ghowoght/mecanum-car/Src/general/dt.h

/**
 * @file dt.h
 * @brief 数据传输程序
 * @author Linfu Wei (ghowoght@qq.com)
 * @version 1.0
 * @date 2020-12-27
 * 
 * @copyright Copyright (c) 2020  WHU-EIS
 * 
 */
#ifndef __DT_H_
#define __DT_H_
#include "stm32g4xx_hal.h"

extern uint8_t data_receive[100];
extern uint8_t data_one_byte[1];
void GetOneByte(uint8_t data);
void DataDecoder(uint8_t *data);

extern UART_HandleTypeDef hlpuart1;
extern UART_HandleTypeDef huart1;
void DataTrans(void);
void DataTrans_IMU_Raw(void);
void DataTrans_UserData(void);
void DataTrans_Odom(void);
void DataTrans_Task(uint32_t dT_ms);


#endif
