ghowoght/mecanum-car/SensorDriver/IIC/IOI2C.h

#ifndef __IOI2C_H
#define __IOI2C_H
#include "sys.h"
 
extern volatile u8 I2C_FastMode;

//IO方向设置
#define SDA_IN()  {GPIOC->MODER&=~(3<<(7*2));GPIOC->MODER|=0<<7*2;}	
#define SDA_OUT() {GPIOC->MODER&=~(3<<(7*2));GPIOC->MODER|=1<<7*2;} 	
//void SDA_IN(void);
//void SDA_OUT(void);


//IO操作函数	 
#define IIC_SCL    PCout(6) //SCL
#define IIC_SDA    PCout(7) //SDA	 
#define READ_SDA   PCin(7)  //输入SDA 

//IIC所有操作函数 
int IIC_Start(void);				//发送IIC开始信号
void IIC_Stop(void);	  			//发送IIC停止信号
void IIC_Send_Byte(u8 txd);			//IIC发送一个字节
u8 IIC_Read_Byte(unsigned char ack);//IIC读取一个字节
int IIC_Wait_Ack(void); 				//IIC等待ACK信号
void IIC_Ack(void);					//IIC发送ACK信号
void IIC_NAck(void);				//IIC不发送ACK信号

void IIC_Write_One_Byte(u8 daddr,u8 addr,u8 data);
u8 IIC_Read_One_Byte(u8 daddr,u8 addr);	 
unsigned char I2C_Readkey(unsigned char I2C_Addr);

unsigned char I2C_ReadOneByte(unsigned char I2C_Addr,unsigned char addr);
unsigned char IICwriteByte(unsigned char dev, unsigned char reg, unsigned char data);
u8 IICwriteBytes(u8 dev, u8 reg, u8 length, u8* data);
u8 IICwriteBits(u8 dev,u8 reg,u8 bitStart,u8 length,u8 data);
u8 IICwriteBit(u8 dev,u8 reg,u8 bitNum,u8 data);
u8 IICreadBytes(u8 dev, u8 reg, u8 length, u8 *data);

int i2cWrite(uint8_t addr, uint8_t reg, uint8_t len, uint8_t *data);
int i2cRead(uint8_t addr, uint8_t reg, uint8_t len, uint8_t *buf);

#endif

//------------------End of File----------------------------
