ghowoght/mecanum-car/Src/general/Scheduler.h

/* Define to prevent recursive inclusion -------------------------------------*/
#ifndef _SCHEDULER_H_
#define _SCHEDULER_H_


/* Includes ------------------------------------------------------------------*/
#include "sys.h"
/* Exported types ------------------------------------------------------------*/


typedef struct
{
	void(*task_func)(u32 dT_us);
//	u16 rate_hz;
	int interval_ticks;
	uint64_t last_run;
}sched_task_t;

/* Exported constants --------------------------------------------------------*/
/* Exported macro ------------------------------------------------------------*/
/* Exported functions ------------------------------------------------------- */

//static 
uint32_t GetSysRunTimeUs(void);
//user
u8 Main_Task(void);
void INT_1ms_Task(void);
#endif
