ghowoght/mecanum-car/Src/general/sys.h

#ifndef _SYS_H_
#define _SYS_H_
#include "stm32g4xx_hal.h"
#include <stdint.h>

typedef uint32_t  u32;
typedef uint16_t u16;
typedef uint8_t  u8;
typedef int32_t  s32;
typedef int16_t  s16;
typedef int8_t   s8;

#endif
